jhester/micro-ekho/mobile/www/jquery.mobile-1.4.5/demos/_assets/img/firefox_os.png

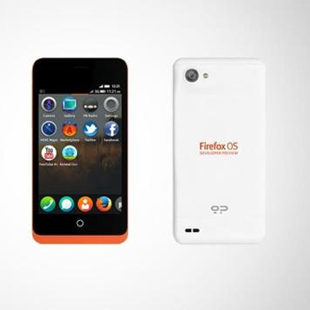
mobile/www/jquery.mobile-1.4.5/demos/_assets/img/firefox_os.png
