jhester/micro-ekho/mobile/www/jquery.mobile-1.4.5/demos/_assets/img/galaxy_express.png

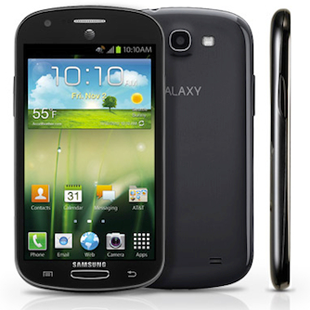
mobile/www/jquery.mobile-1.4.5/demos/_assets/img/galaxy_express.png
