jhester/micro-ekho/mobile/www/jquery.mobile-1.4.5/demos/_assets/img/lumia_800.png

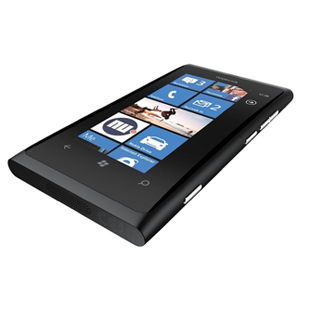
mobile/www/jquery.mobile-1.4.5/demos/_assets/img/lumia_800.png
