jhester/micro-ekho/mobile/www/jquery.mobile-1.4.5/demos/_assets/img/photo-landscape.jpg

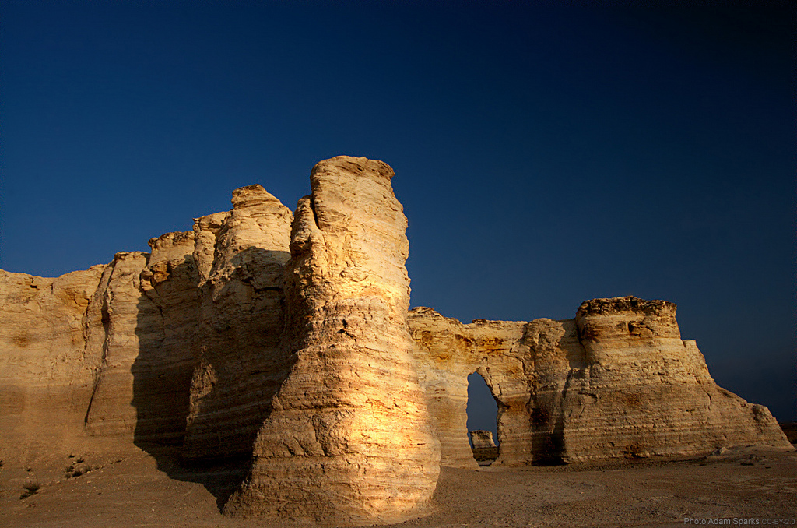
mobile/www/jquery.mobile-1.4.5/demos/_assets/img/photo-landscape.jpg
